makerbase-mks/MKS-H43/Images/H43_GEN_L.jpg

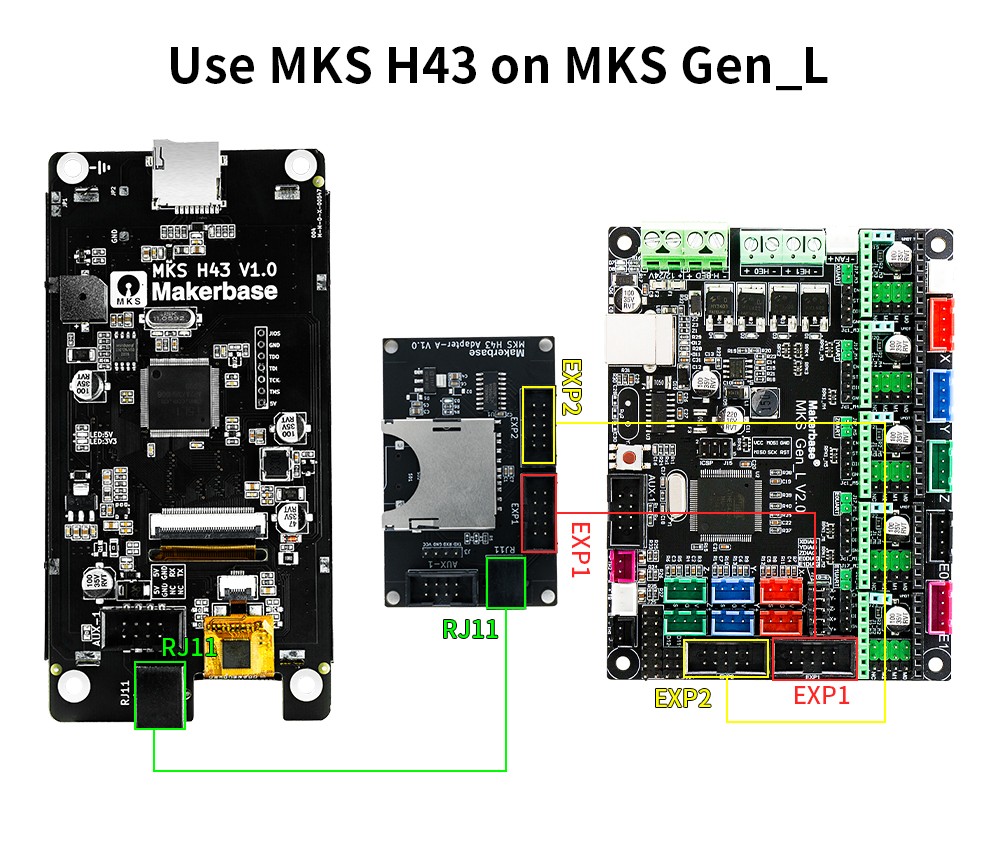
Images/H43_GEN_L.jpg
