makerbase-mks/MKS-H43/Images/H43_ROBIN_NANO_V1_V2.jpg

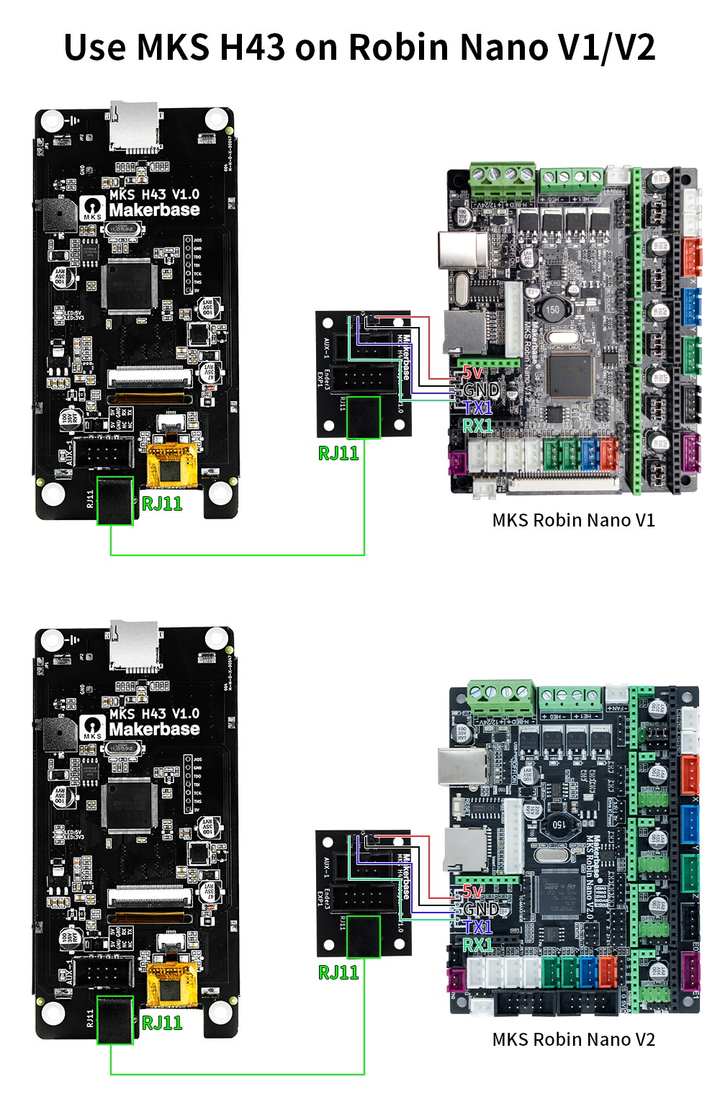
Images/H43_ROBIN_NANO_V1_V2.jpg
