makerbase-mks/MKS-H43/Images/H43_SGEN_L.jpg

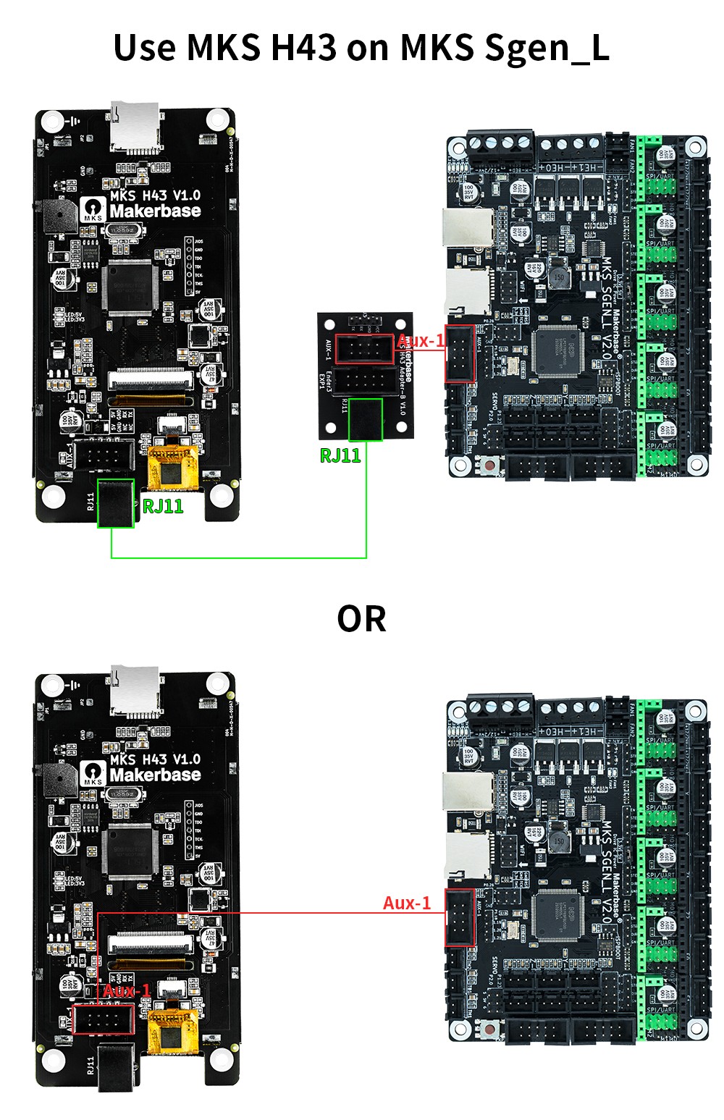
Images/H43_SGEN_L.jpg
