makerbase-mks/MKS-H43/Images/H43_SKR.jpg

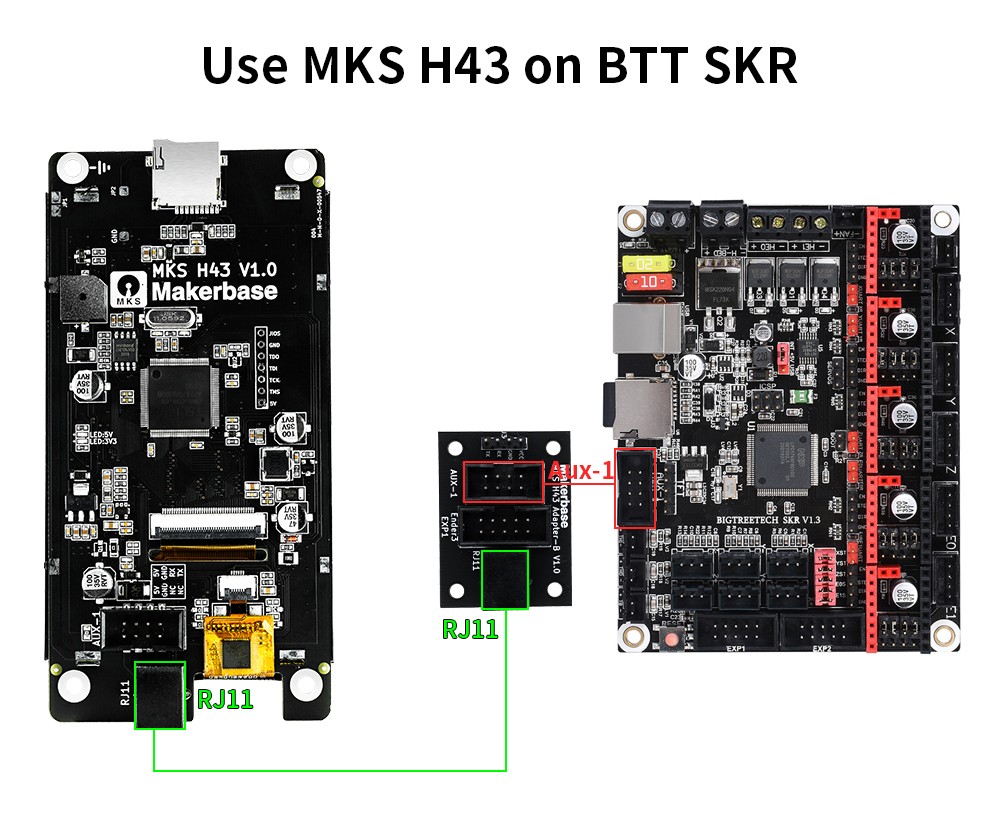
Images/H43_SKR.jpg
